DasBasti/NokiaRetroFit/Documentation/Display/1.44串口红板/模块原理图.pdf

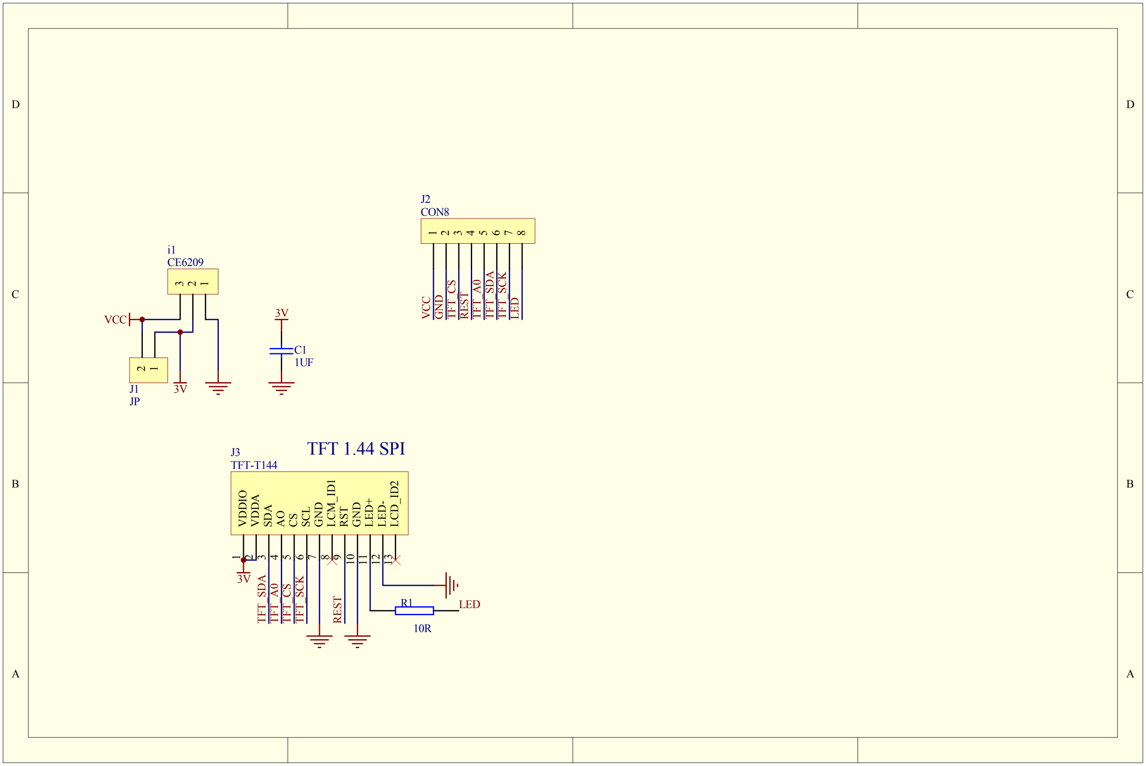
[picture p3: figure]
ABC; CBA; TFT 1.44 SPI; LED; TFT_SDA; TFT_A0; TFT_SCK; REST; TFT_CS; VCC; GND; J2 CON8; VDDIO 1 VDDA 2 SDA 3 AO 4 CS 5; SCL 6; GND 7; LCM_ID1 8; RST 9; GND 10; LED+ 11 LED- 12; LCD_ID2 13; J3 TFT-T144
