DasBasti/NokiaRetroFit/Datasheets/14b2a-sim_cards_with_128mb_memory.jpg

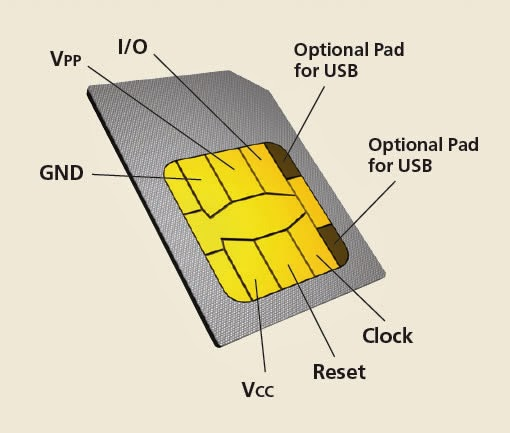
Datasheets/14b2a-sim_cards_with_128mb_memory.jpg
