DasBasti/NokiaRetroFit/Datasheets/Image 1.png

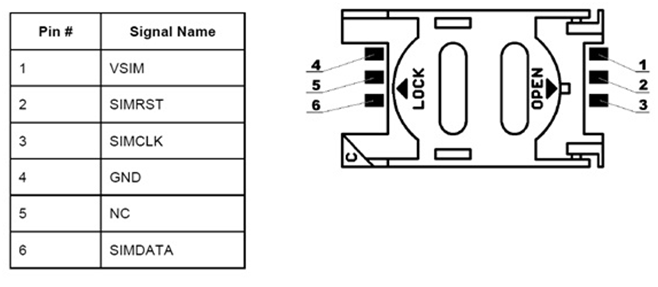
Datasheets/Image 1.png
