DasBasti/NokiaRetroFit/Documentation/thumbnail.png

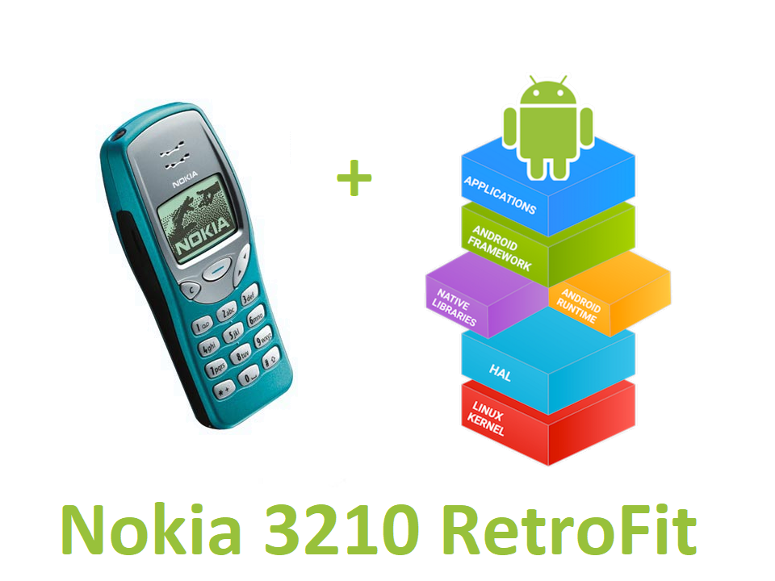
Documentation/thumbnail.png
