DasBasti/NokiaRetroFit/Documentation/Pictures/frontside_angle_no_components.png

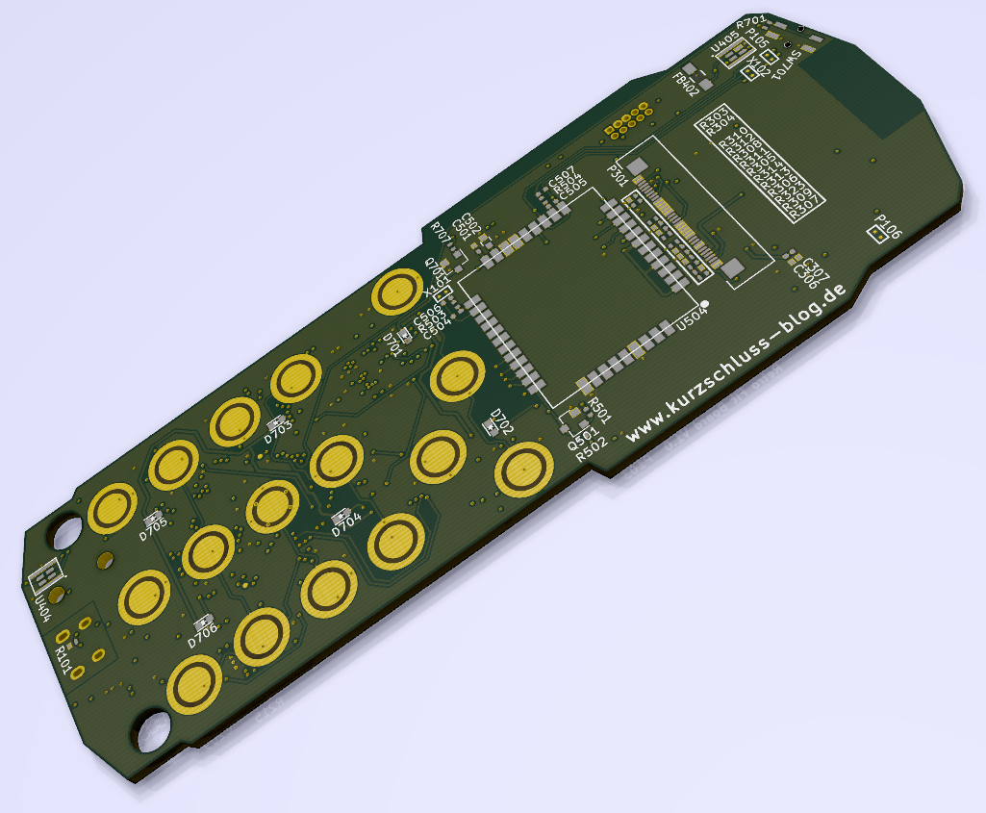
Documentation/Pictures/frontside_angle_no_components.png
