DasBasti/NokiaRetroFit/Documentation/Display/1.44串口红板/结构.pdf

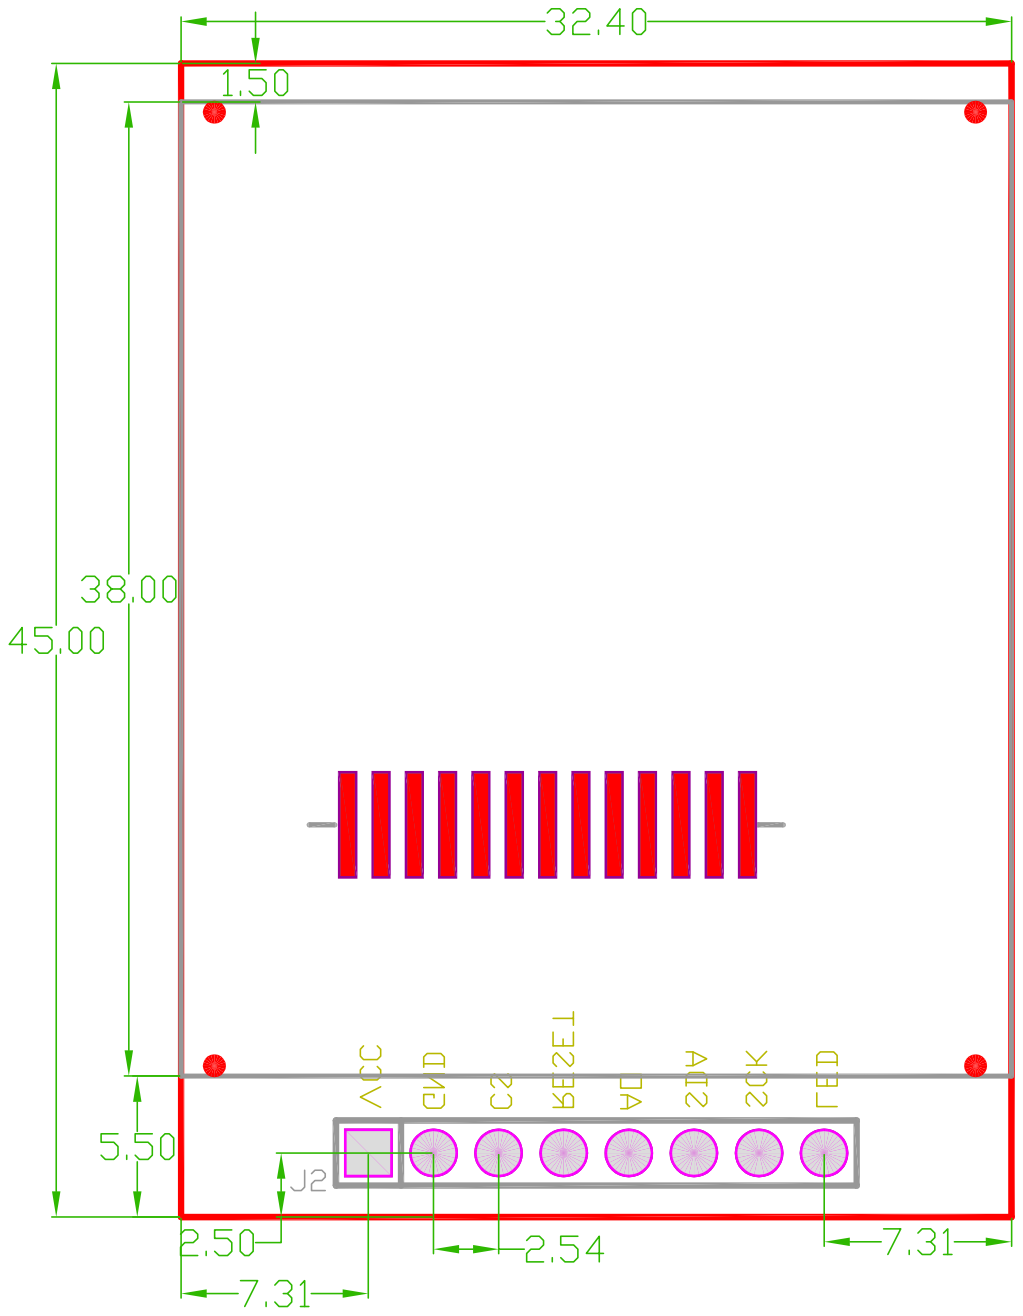
[picture p22: page 1]
